domenicaperex1007-pixel/FdD_E_14/Proyecto/Módulo Mecánico/Certificados/Calva Becerra, Sofia/CertificadosUnidos.pdf

Soa Calva

Introduction to Sketching

April 30, 2026

Soa Calva

Introduction to Part Studios

April 30, 2026

Soa Dayanna Calva Becerra

April 30, 2026

Detailed Drawings

Soa Dayanna Calva Becerra

April 30, 2026

Introduction to Onshape Assemblies

Soa Dayanna Calva Becerra

Advanced Onshape Assemblies

May 21, 2026
