domenicaperex1007-pixel/FdD_E_14/Proyecto/Módulo Mecánico/Certificados/Cayco Tucto, Caleb/CertificadosUnidos.pdf

Caleb tucto

Introduction to Sketching

April 30, 2026

Caleb Cayco Tucto

Introduction to Part Studios

April 30, 2026

Caleb Cayco Tucto

April 30, 2026

Detailed Drawings

Caleb Cayco Tucto

April 30, 2026

Introduction to Onshape Assemblies

Caleb Cayco Tucto

Advanced Onshape Assemblies

May 21, 2026
