domenicaperex1007-pixel/FdD_E_14/Proyecto/Módulo Mecánico/Certificados/Dulanto Aguilar, Nemesis/CertificadosUnidos.pdf

Nemesis Krystel Dulanto Aguilar

Introduction to Sketching

April 30, 2026

Nemesis Krystel Dulanto Aguilar

Introduction to Part Studios

April 30, 2026

Nemesis Krystel Dulanto Aguilar

April 30, 2026

Detailed Drawings

Nemesis Krystel Dulanto Aguilar

April 30, 2026

Introduction to Onshape Assemblies

Nemesis Krystel Dulanto Aguilar

Advanced Onshape Assemblies

May 21, 2026
