domenicaperex1007-pixel/FdD_E_14/Proyecto/Módulo Mecánico/Certificados/Huillca Quispe, Kevin/CertificadosUnidos.pdf

Kevin Huillca

Introduction to Sketching

April 30, 2026

Kevin Huillca

Introduction to Part Studios

April 30, 2026

Kevin Huillca

April 30, 2026

Detailed Drawings

Kevin Huillca

April 30, 2026

Introduction to Onshape Assemblies

Kevin Huillca

Advanced Onshape Assemblies

May 21, 2026
