domenicaperex1007-pixel/FdD_E_14/Proyecto/Módulo Mecánico/Certificados/Perez Suarez, Doménica/CertificadosUnidos.pdf

Doménica Tiziana Ximena Pérez Suárez

Introduction to Sketching

April 30, 2026

Doménica Tiziana Ximena Pérez Suárez

Introduction to Part Studios

April 30, 2026

Doménica Tiziana Ximena Pérez Suárez

April 30, 2026

Detailed Drawings

Doménica Tiziana Ximena Pérez Suárez

April 30, 2026

Introduction to Onshape Assemblies

Doménica Tiziana Ximena Pérez Suárez

Advanced Onshape Assemblies

May 21, 2026
