domenicaperex1007-pixel/FdD_E_14/Proyecto/Módulo Mecánico/V1.0/Bocetos/Boceto isométricoA V1.0.png

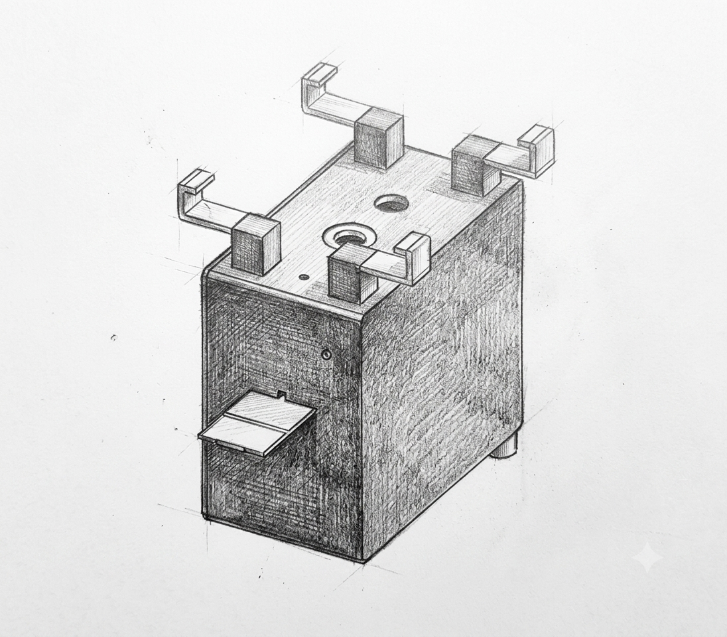
Proyecto/Módulo Mecánico/V1.0/Bocetos/Boceto isométricoA V1.0.png
