domenicaperex1007-pixel/FdD_E_14/Proyecto/Módulo Mecánico/VFINAL/Bocetos/Boceto isométricoA VFINAL.png

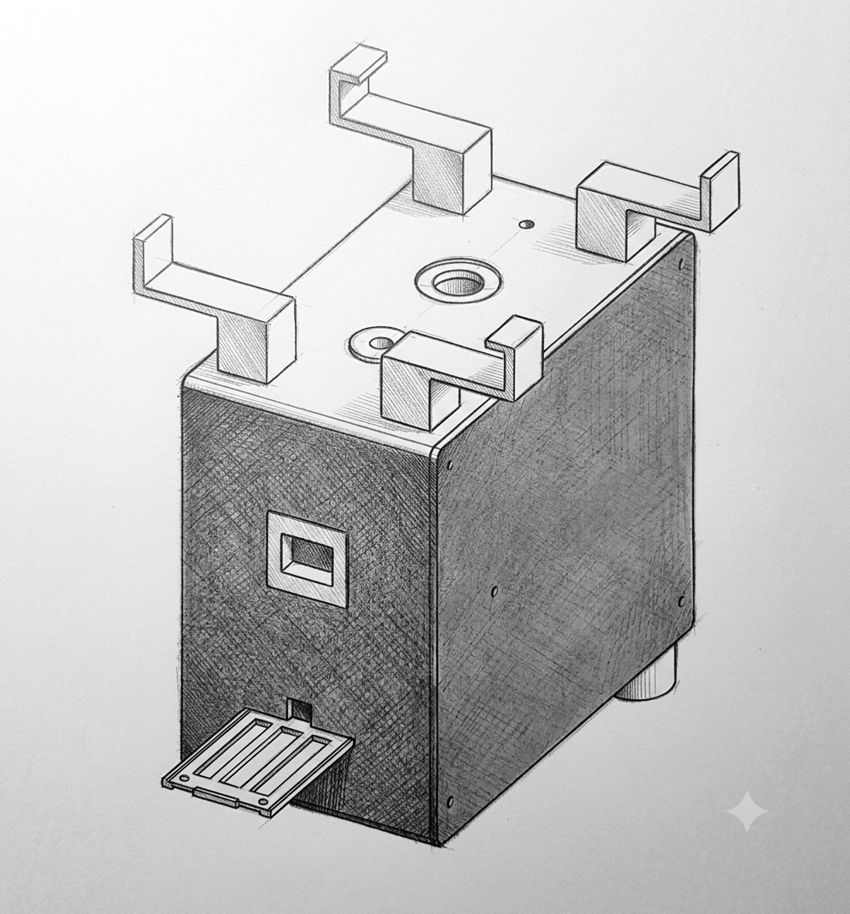
Proyecto/Módulo Mecánico/VFINAL/Bocetos/Boceto isométricoA VFINAL.png
