domenicaperex1007-pixel/FdD_E_14/Proyecto/Módulo Electrónico/V2.0/Esquemático V2.0.pdf

# ESP 32

R1

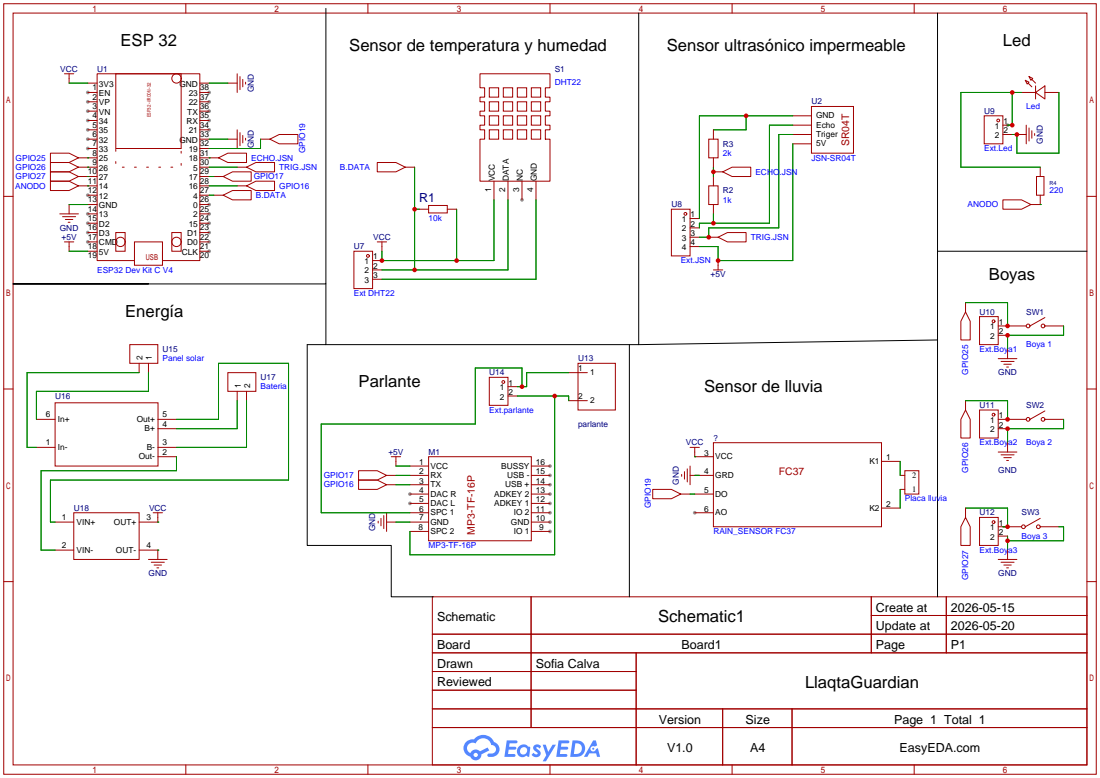
[picture p65: page 1]
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

Schematic | Schematic1 | Create at | 2026-05-15

Update at | 2026-05-20

Board | Board1 | Page | P1
Drawn | Sofia Calva | LlaqtaGuardian
Reviewed

Version | Size | Page 1 Total 1
V1.0 | A4 | EasyEDA.com
