domenicaperex1007-pixel/FdD_E_14/Proyecto/Módulo Mecánico/V1.0/Onshape/Planos/Plano_Estructura en L V1.0.pdf

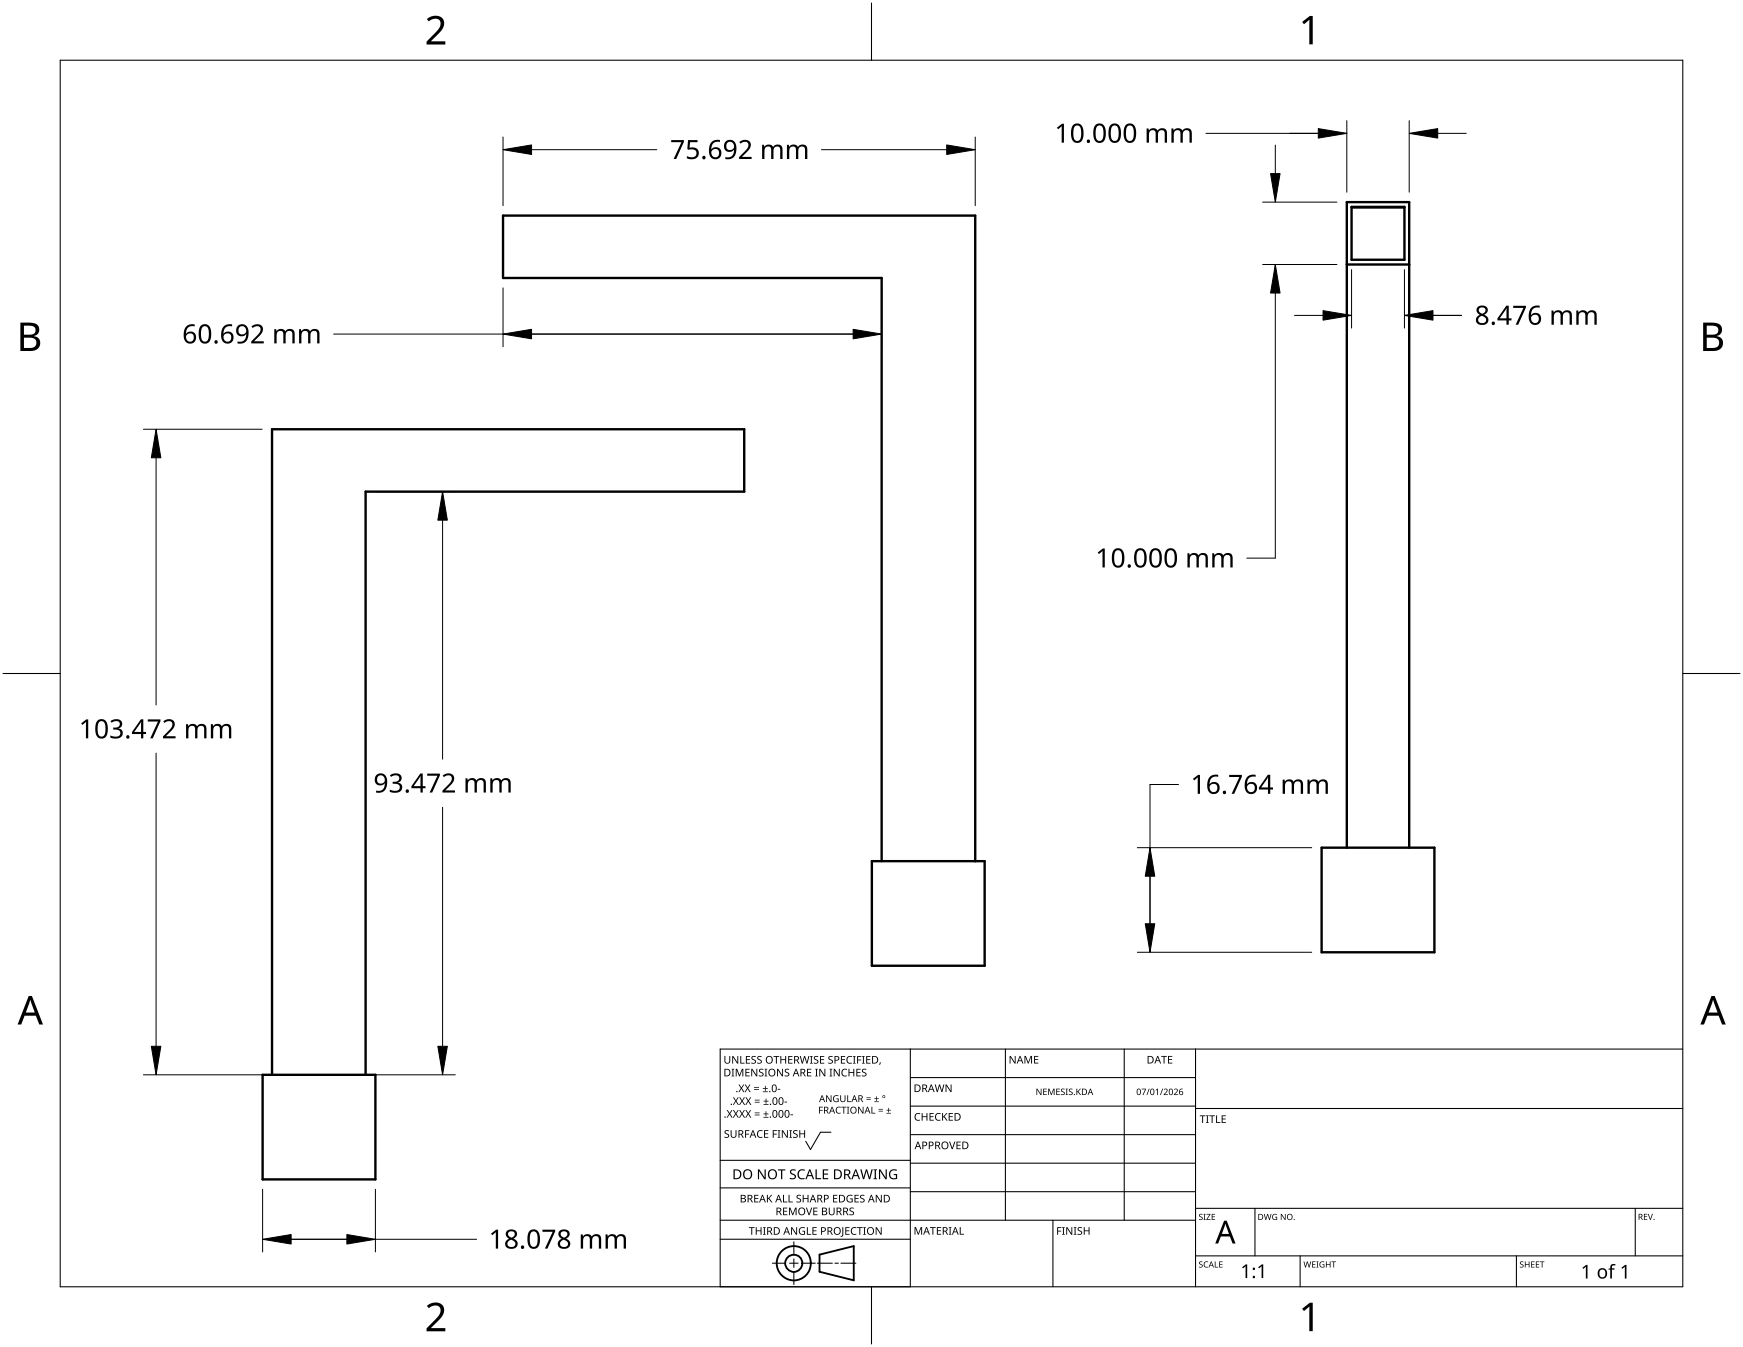
[picture p71: page 1]
