domenicaperex1007-pixel/FdD_E_14/Proyecto/Módulo Mecánico/V1.0/Onshape/Planos/Plano_SoporteFC37 V1.0.pdf

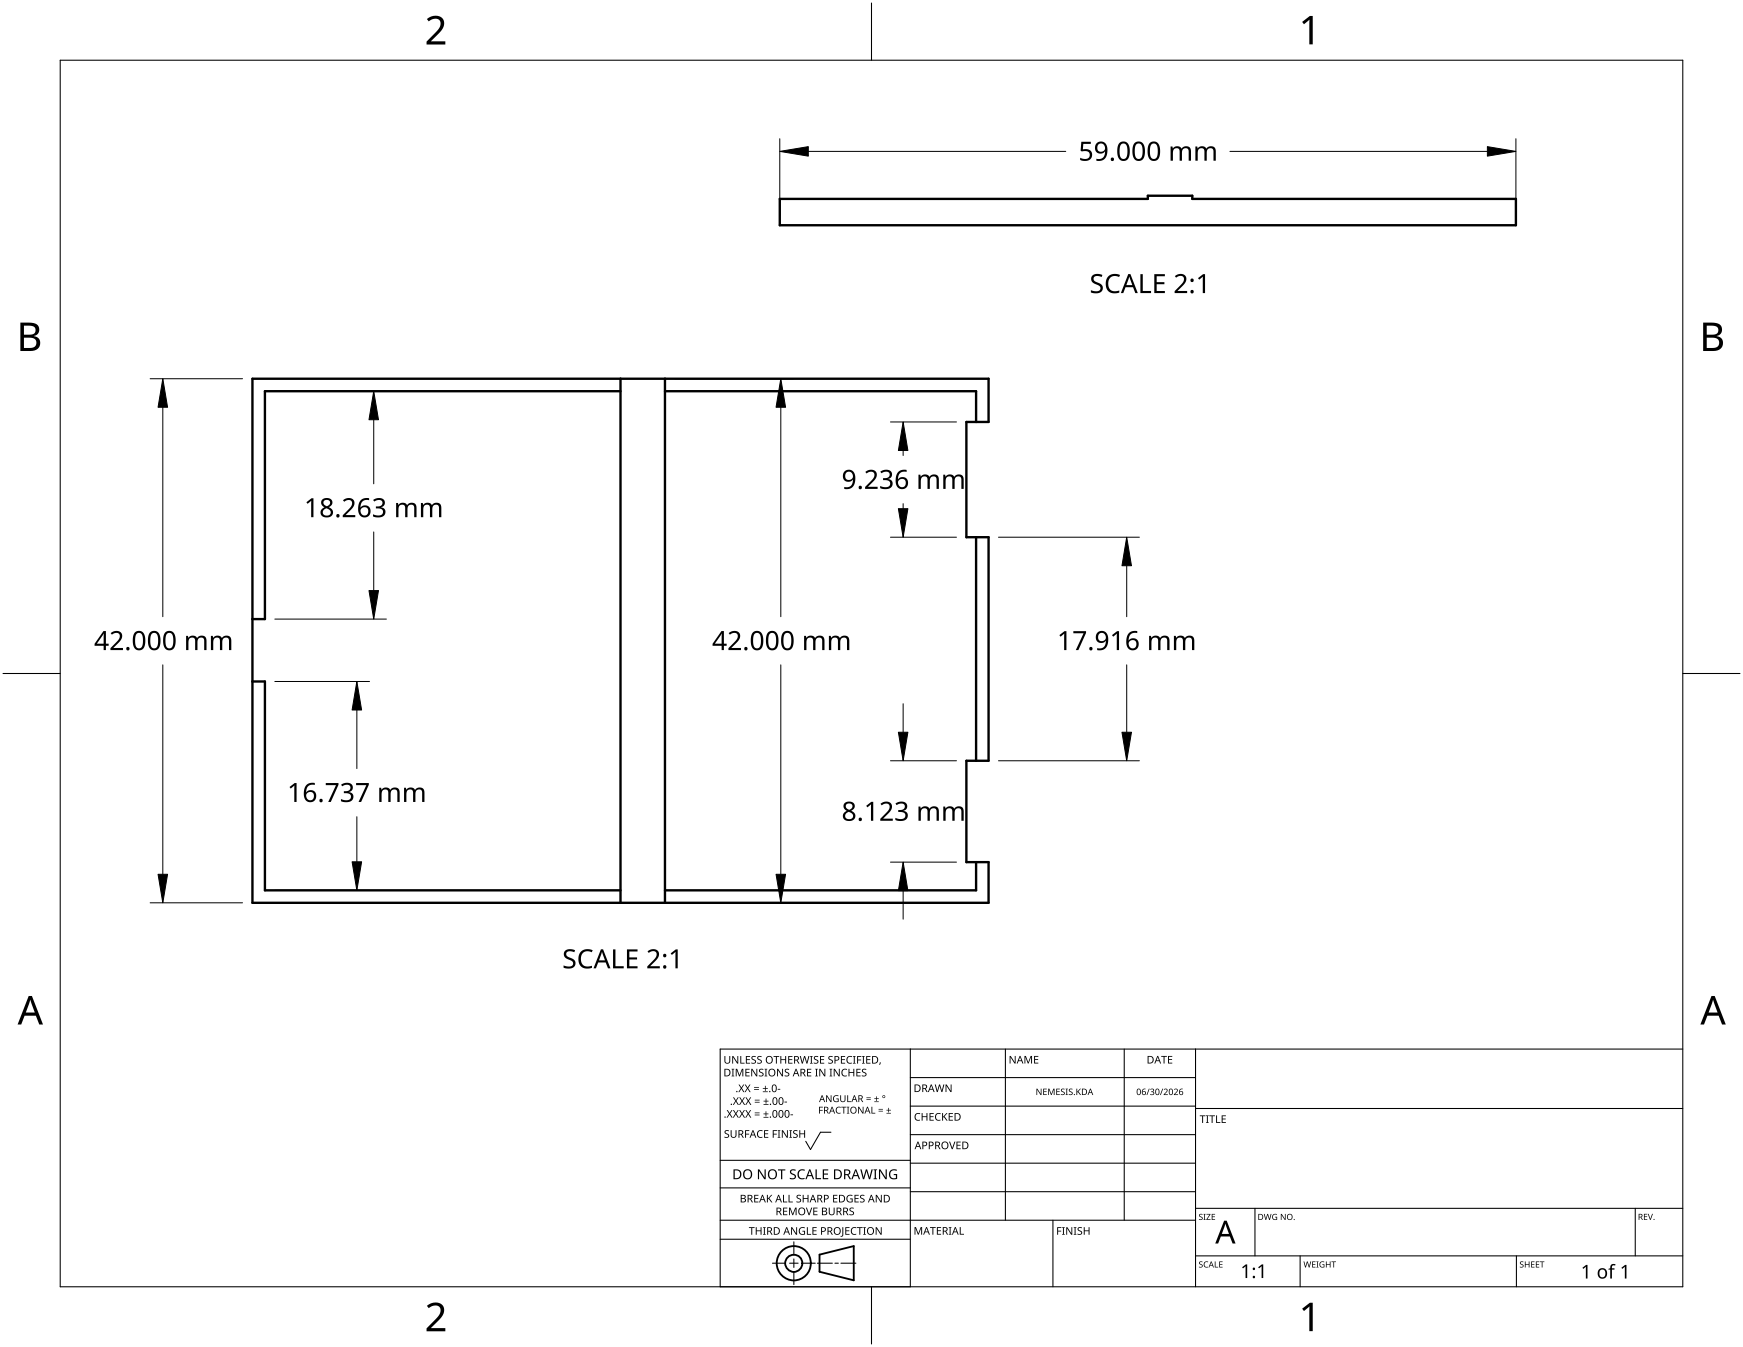
[picture p72: page 1]
