domenicaperex1007-pixel/FdD_E_14/Proyecto/Módulo Mecánico/V1.0/Onshape/Planos/Plano_Caja V1.0.pdf

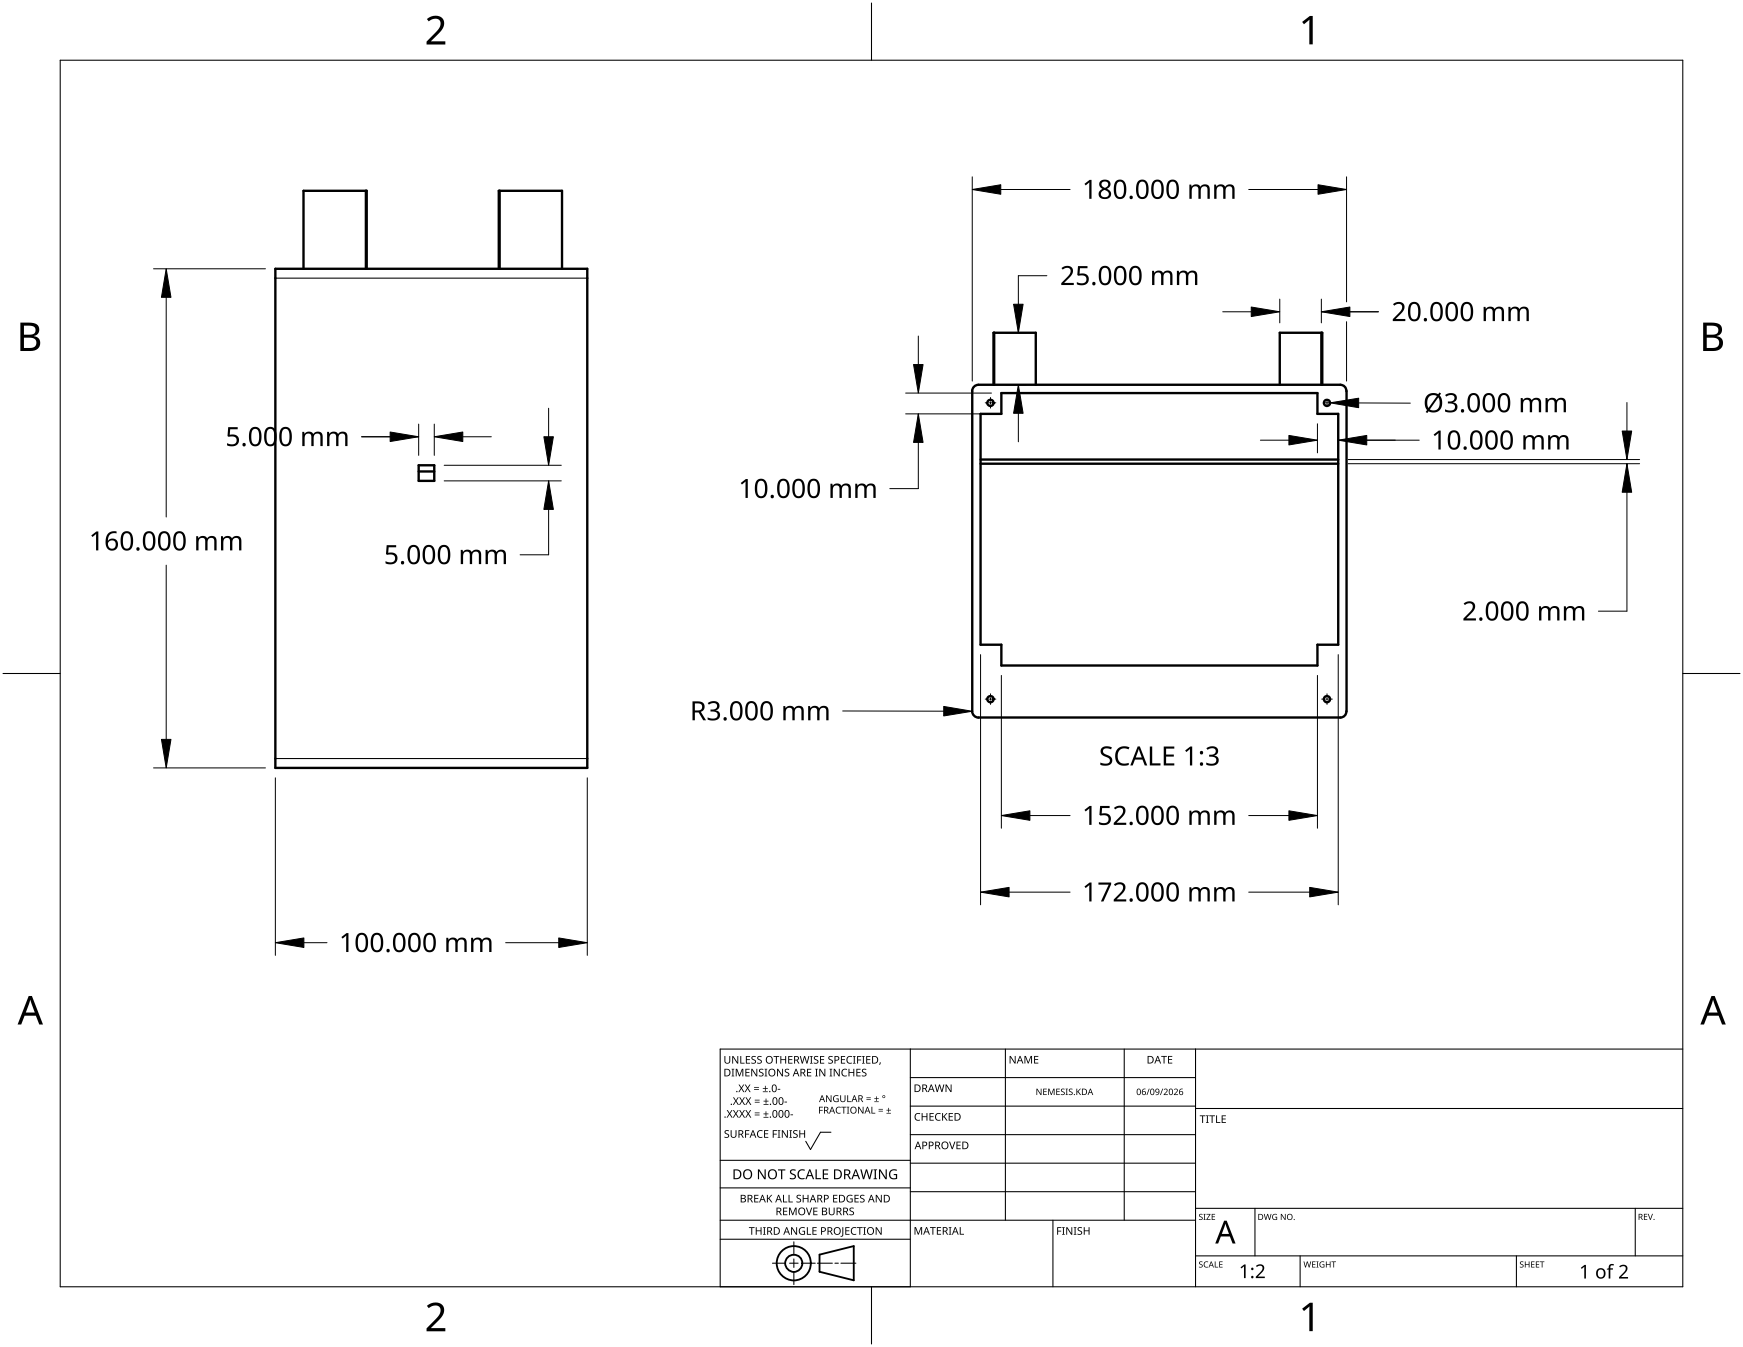
[picture p73: page 1]

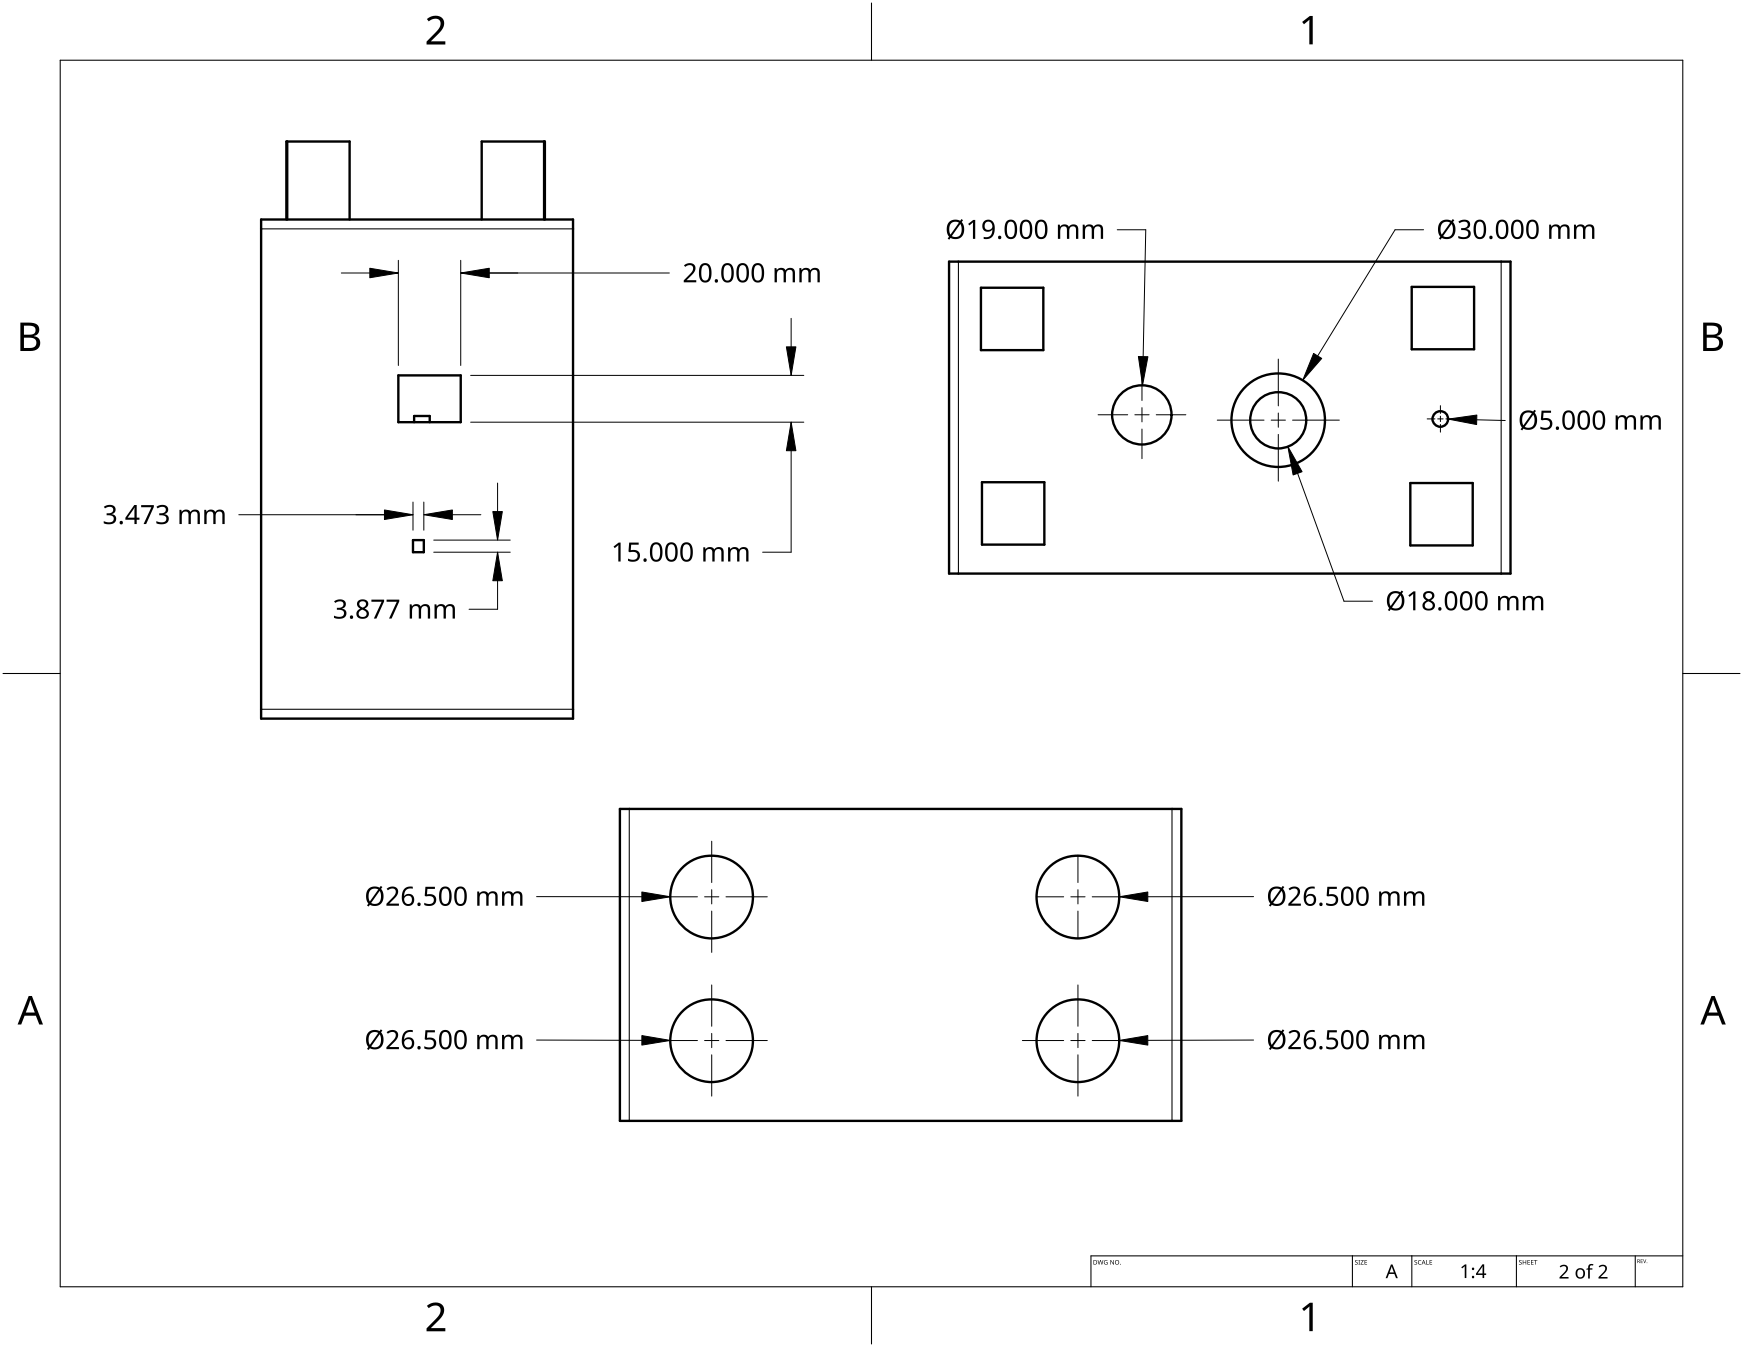
[picture p74: page 2]
