domenicaperex1007-pixel/FdD_E_14/Proyecto/Módulo Mecánico/V1.0/Onshape/Planos/Plano_Puerta V1.0.pdf

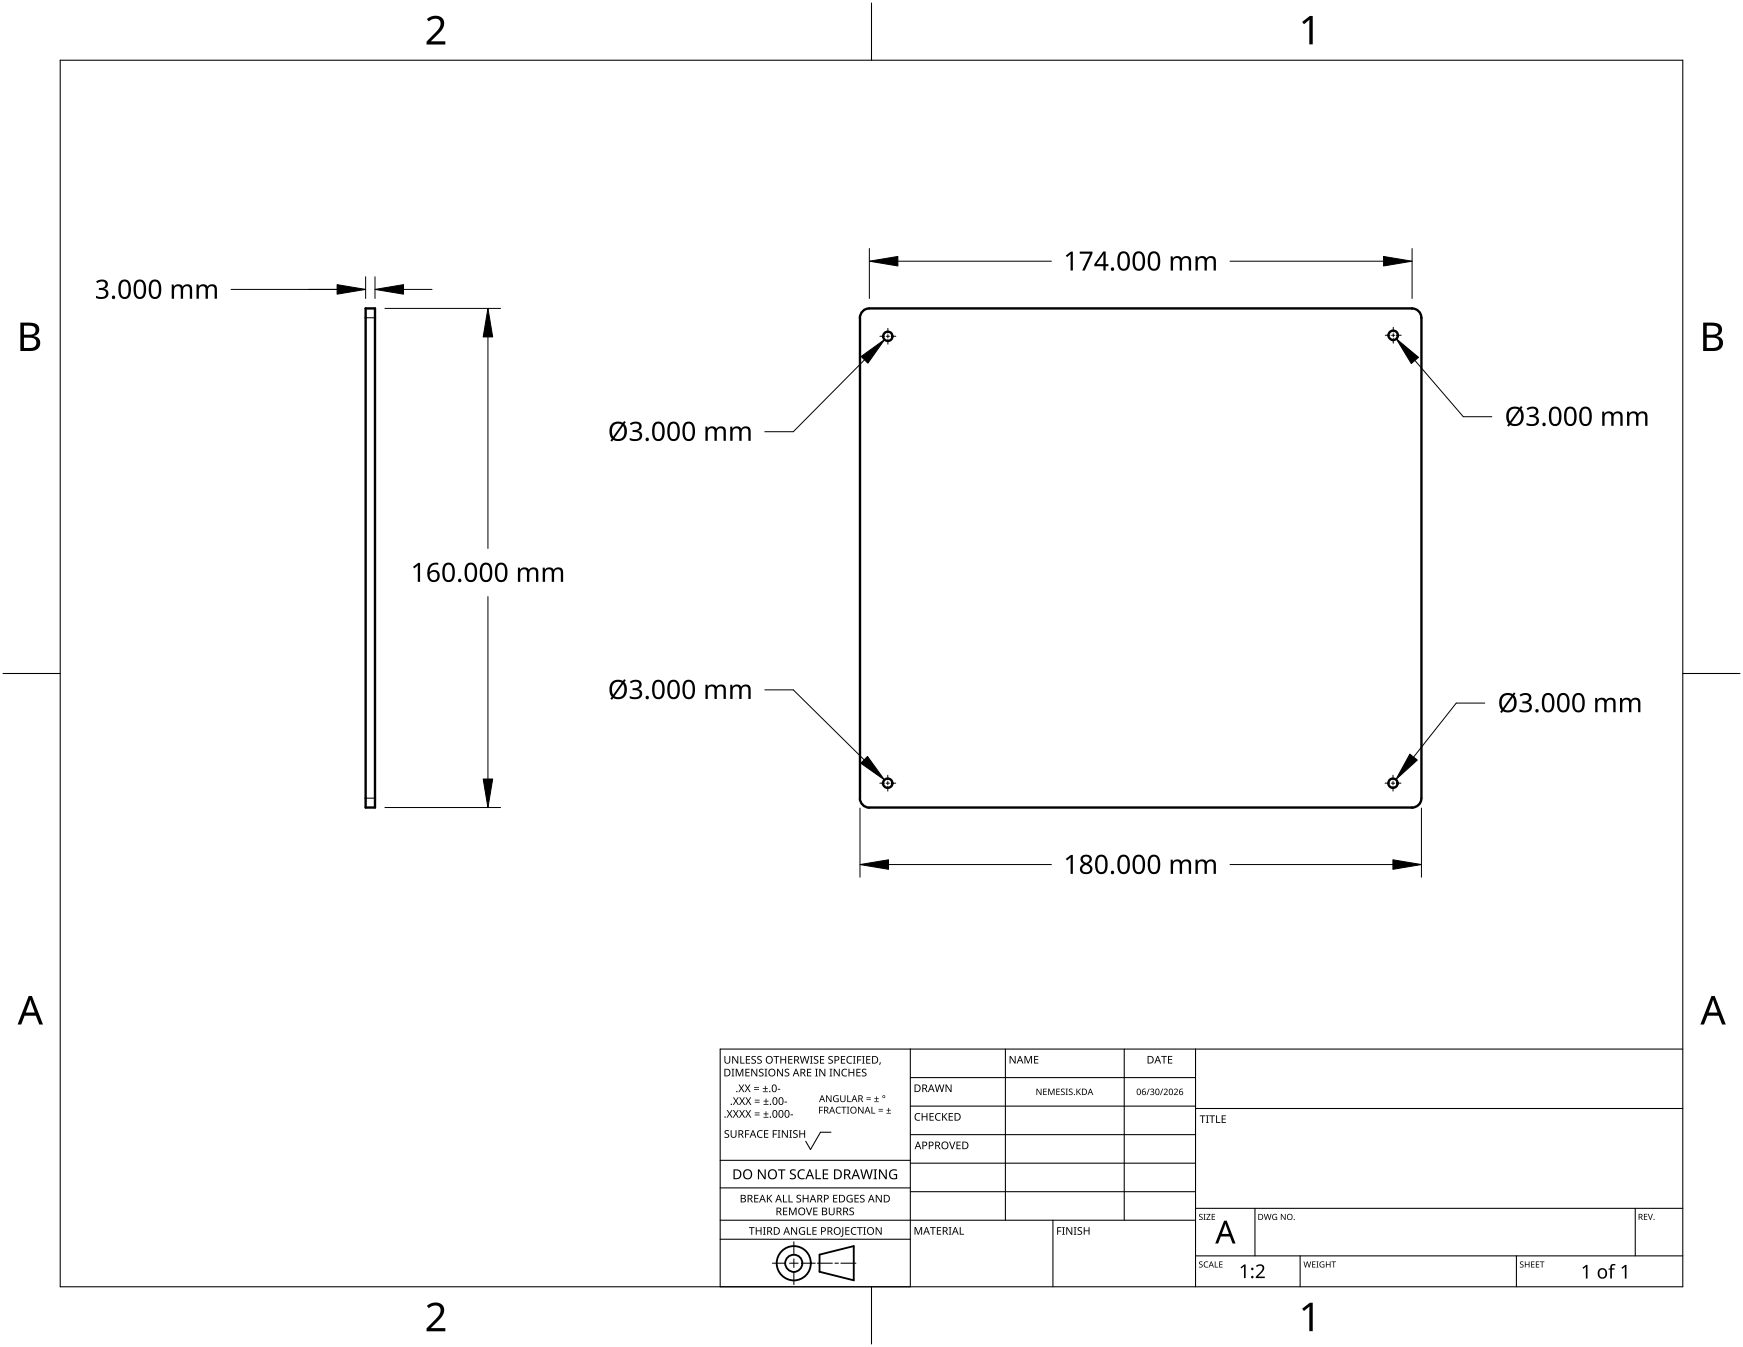
[picture p75: page 1]
