domenicaperex1007-pixel/FdD_E_14/Proyecto/Módulo Mecánico/VFINAL/Onshape/Planos/Plano_Caja VFINAL.pdf

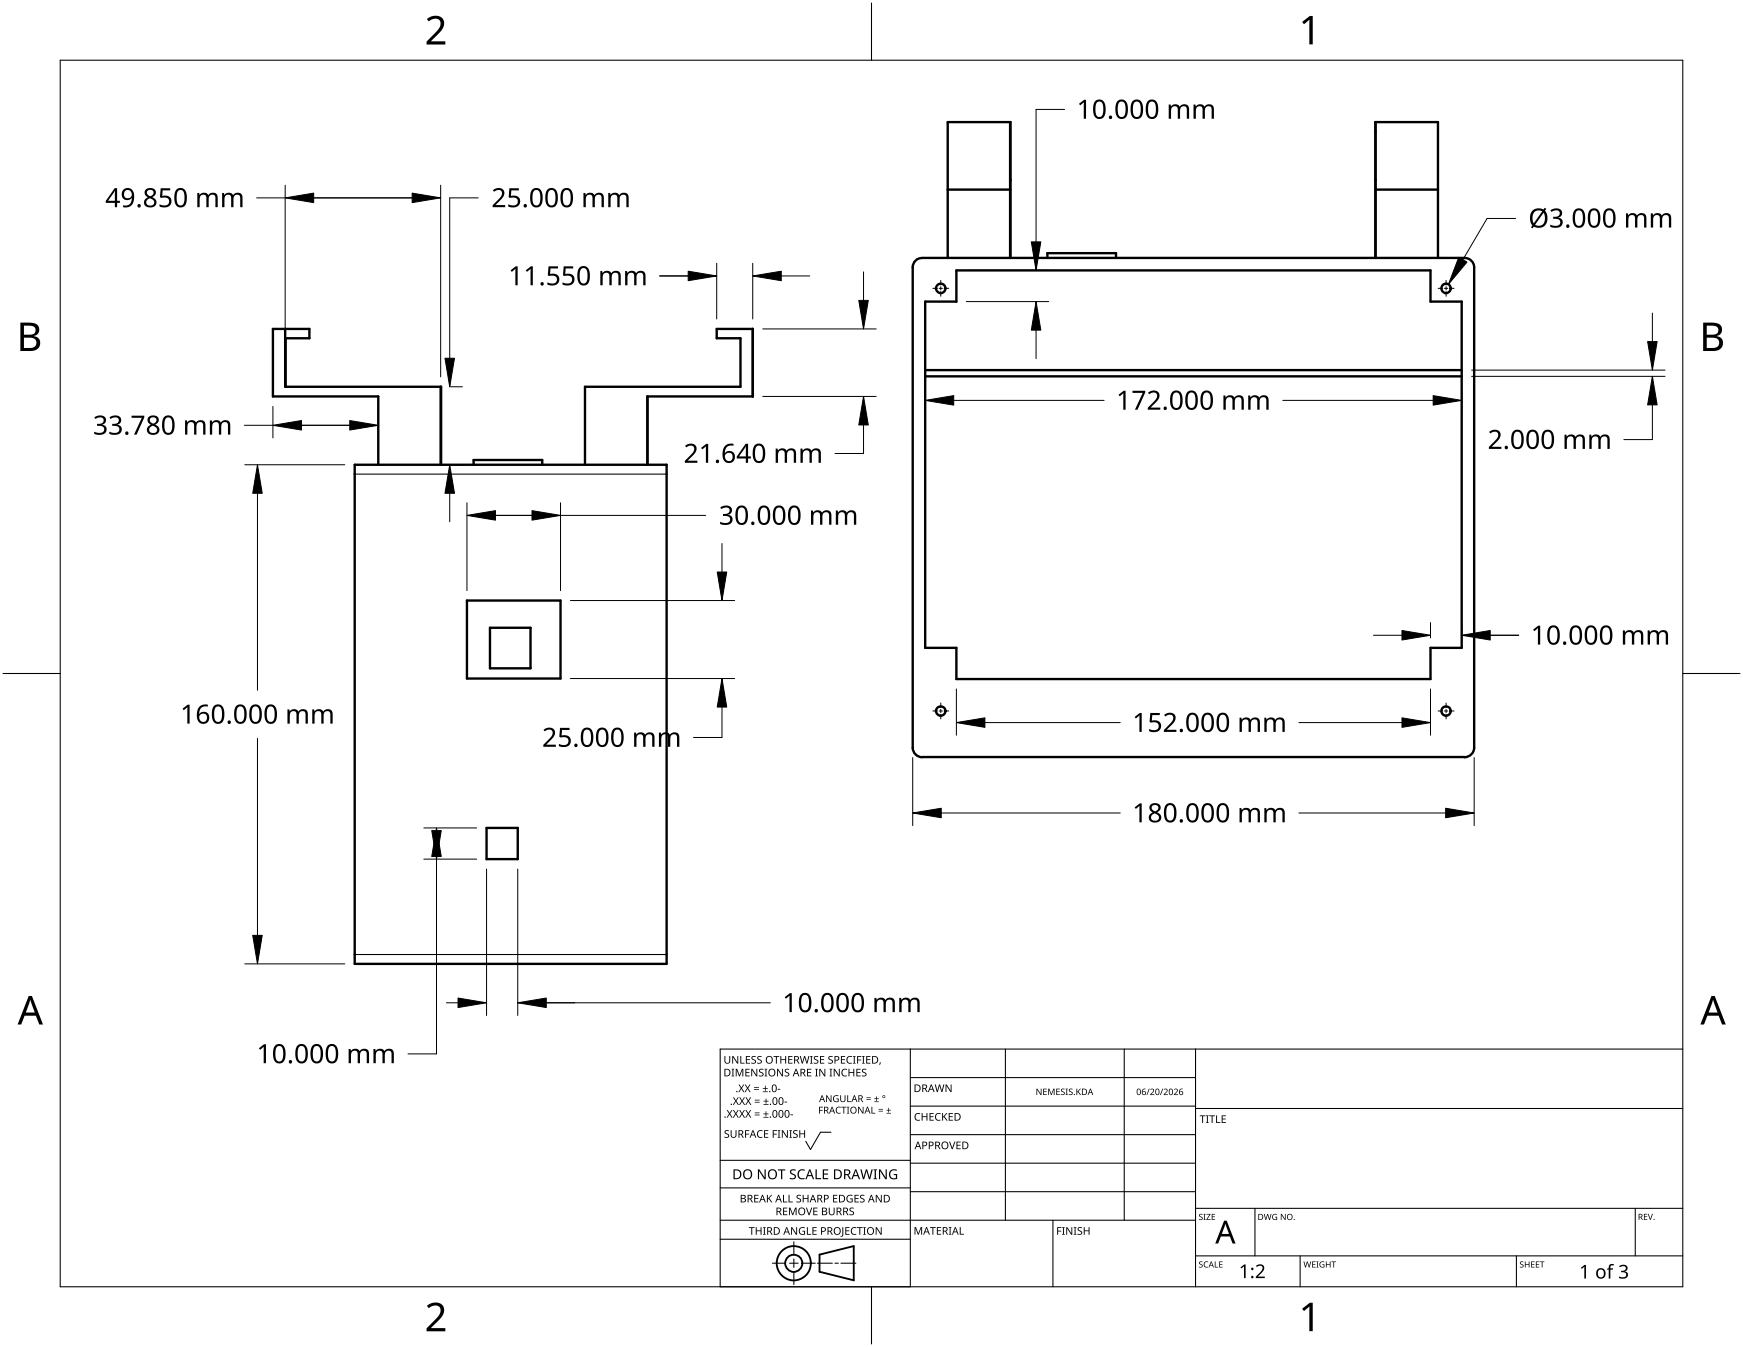
[picture p76: page 1]

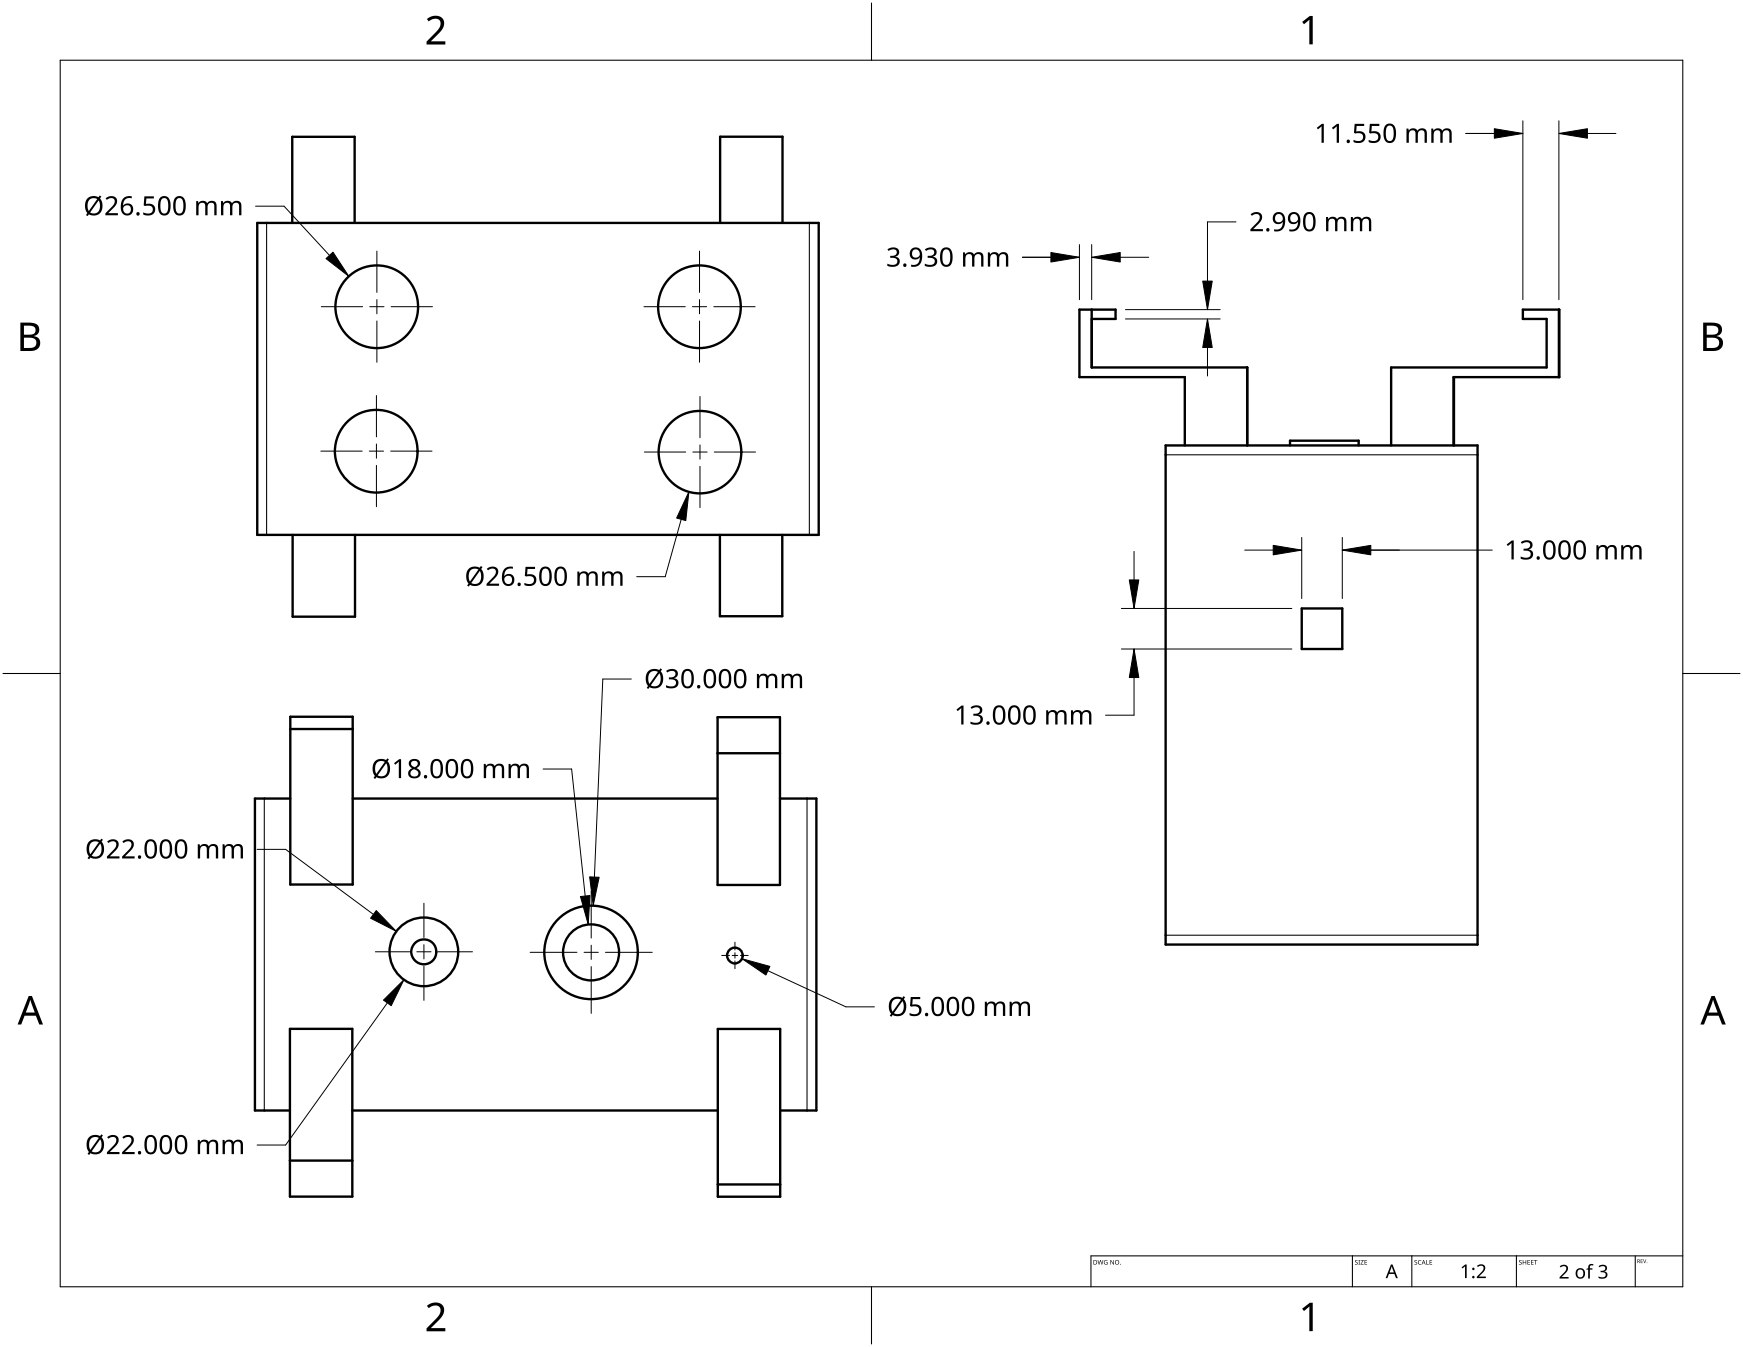
[picture p77: page 2]

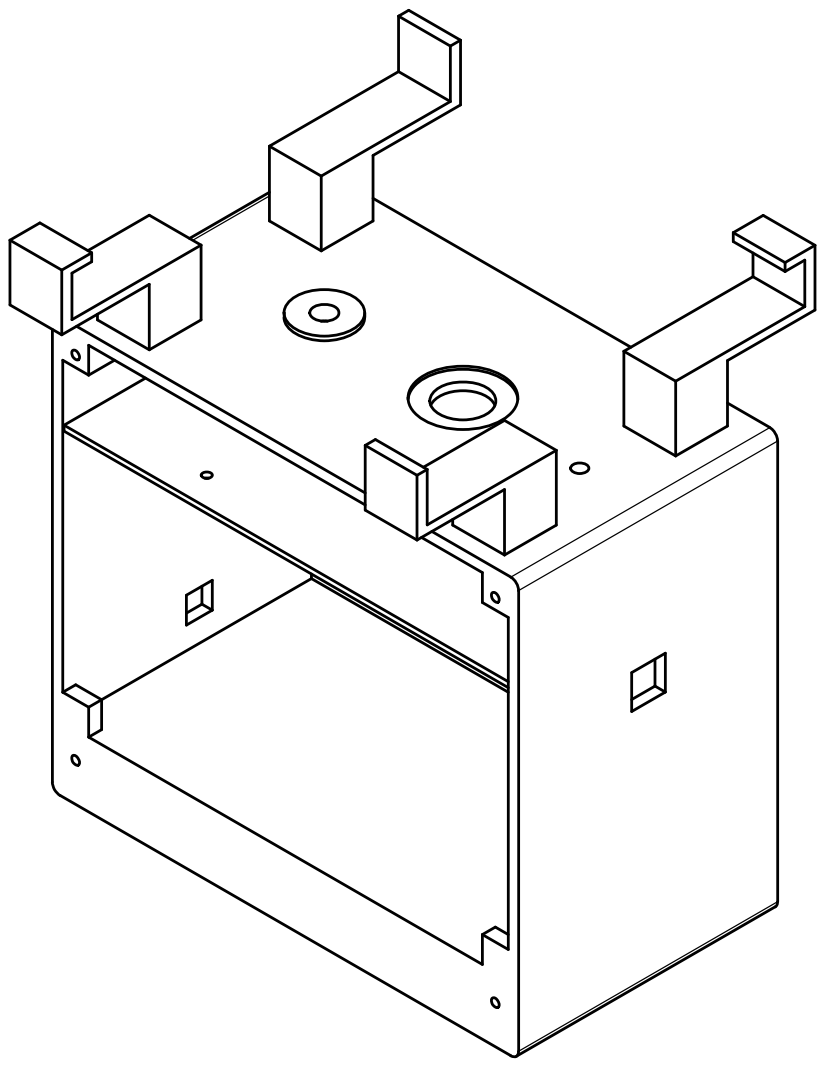
[picture p78: page 3]
