domenicaperex1007-pixel/FdD_E_14/Proyecto/Módulo Mecánico/VFINAL/Onshape/Planos/Plano_Dona VFINAL.pdf

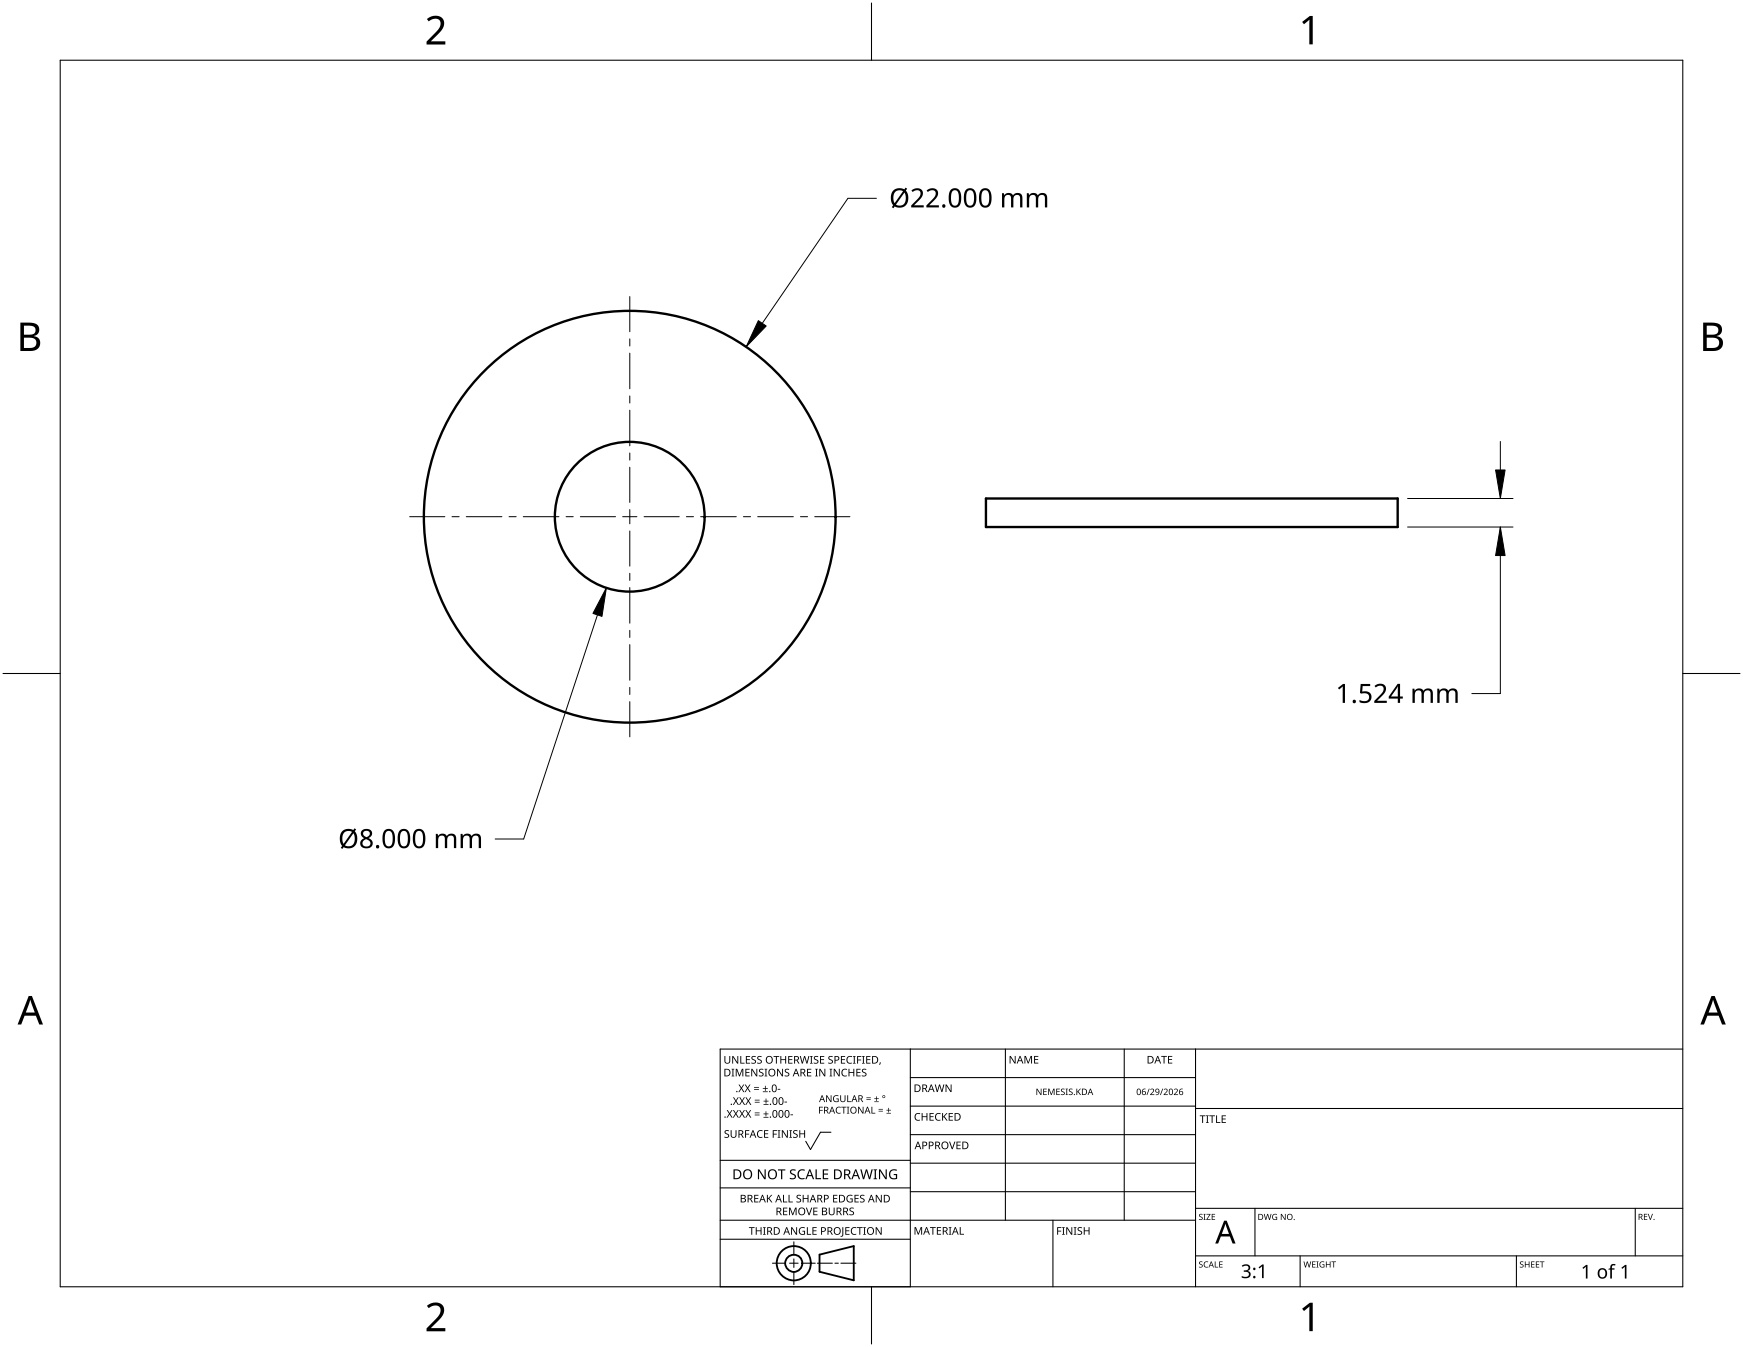
[picture p79: page 1]
