domenicaperex1007-pixel/FdD_E_14/Proyecto/Módulo Mecánico/VFINAL/Onshape/Planos/Plano_Estaca VFINAL.pdf

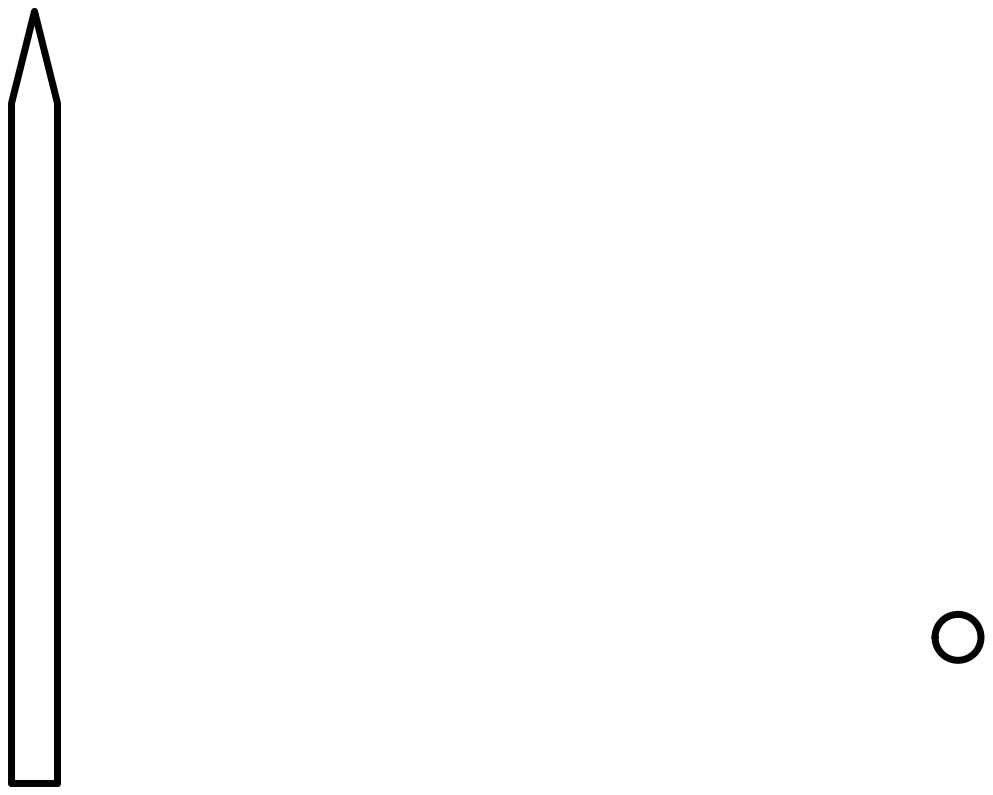
[picture p80: page 1]
