domenicaperex1007-pixel/FdD_E_14/Proyecto/Módulo Mecánico/VFINAL/Onshape/Planos/Plano_Estructura en L VFINAL.pdf

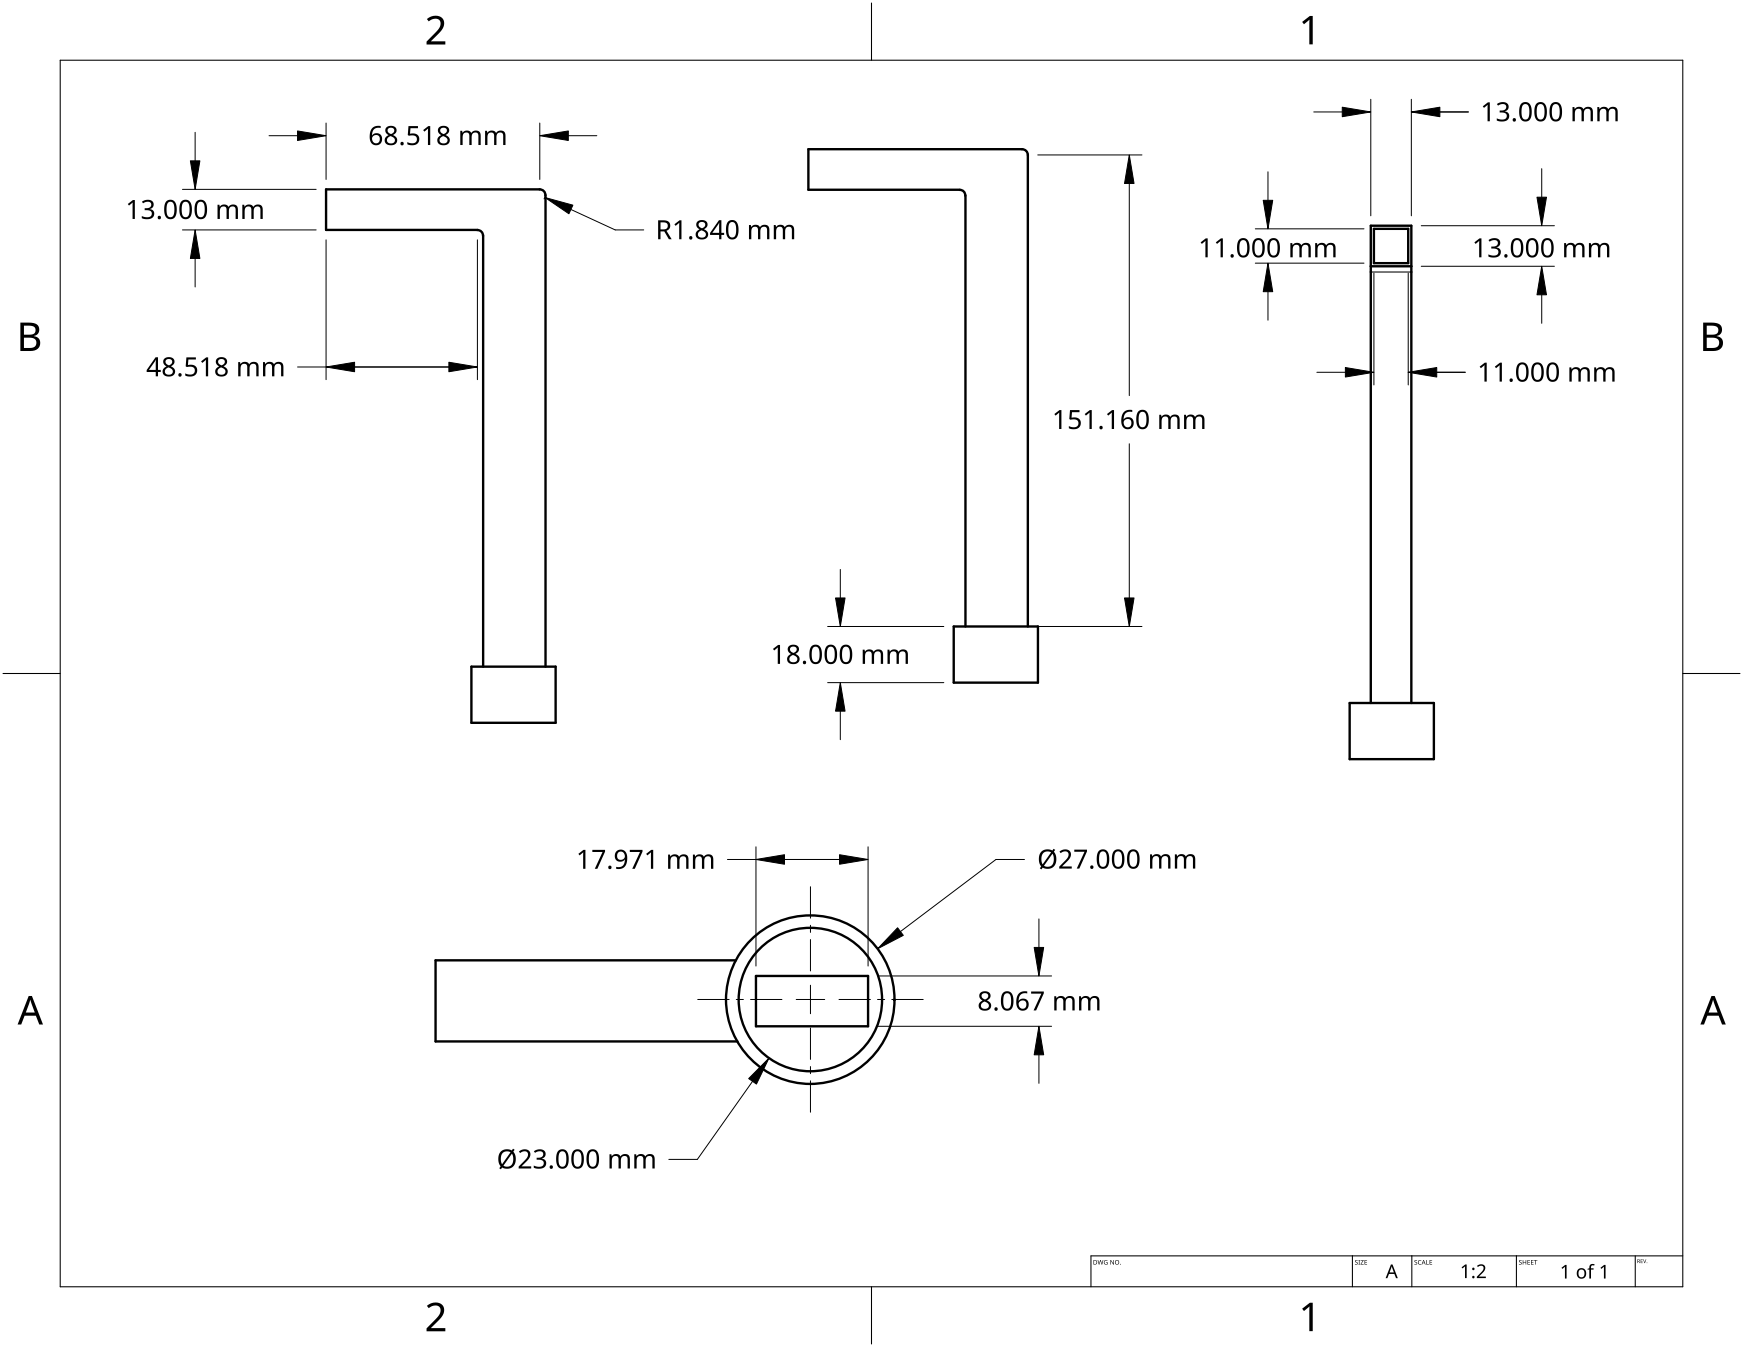
[picture p81: page 1]
