domenicaperex1007-pixel/FdD_E_14/Proyecto/Módulo Mecánico/VFINAL/Onshape/Planos/Plano_Puerta VFINAL.pdf

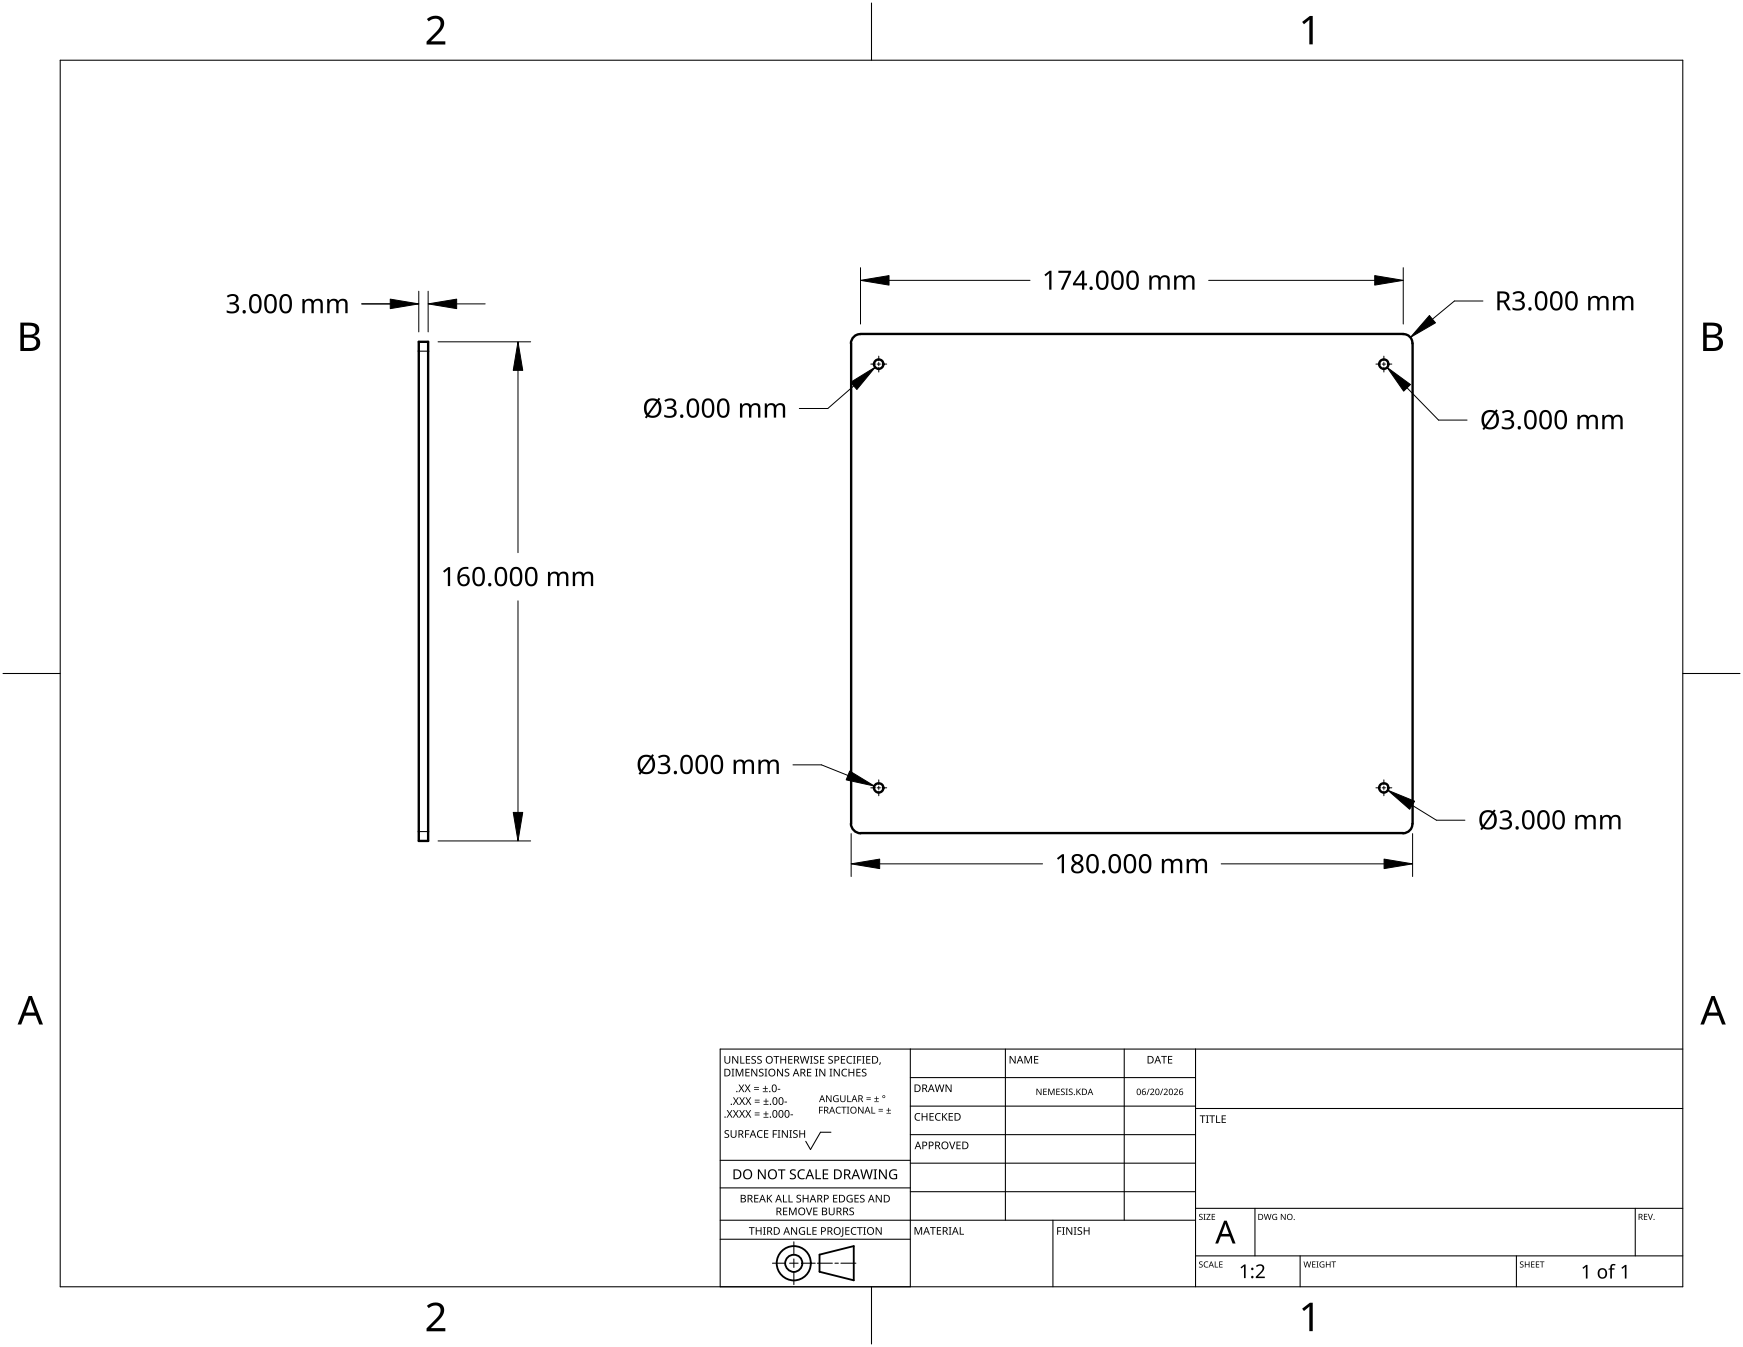
[picture p82: page 1]
