domenicaperex1007-pixel/FdD_E_14/Proyecto/Módulo Mecánico/VFINAL/Onshape/Planos/Plano_SoporteFC37 VFINAL.pdf

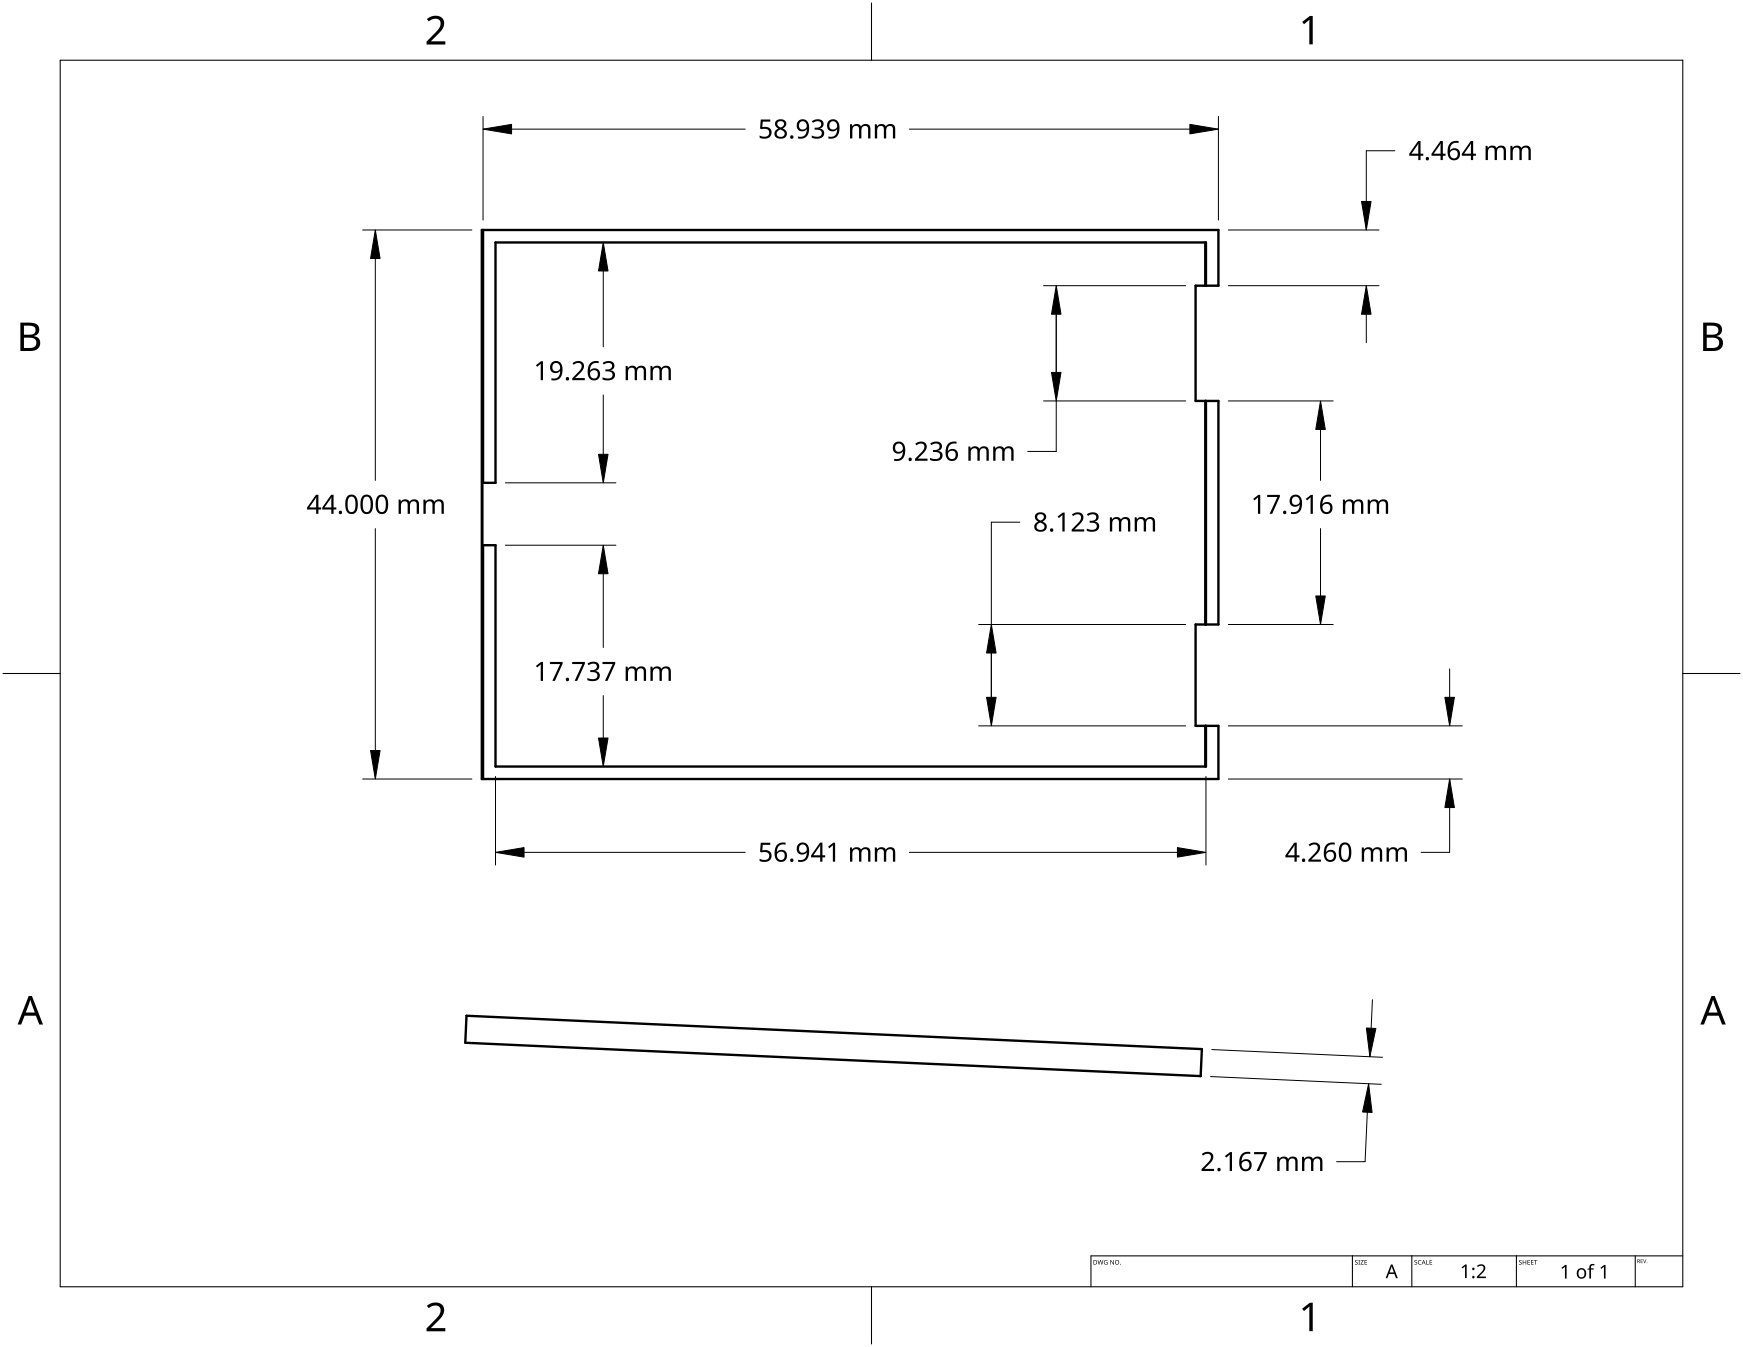
[picture p83: page 1]
