domenicaperex1007-pixel/FdD_E_14/Proyecto/Módulo Mecánico/VFINAL/Onshape/Planos/Plano_Ventana VFINAL.pdf

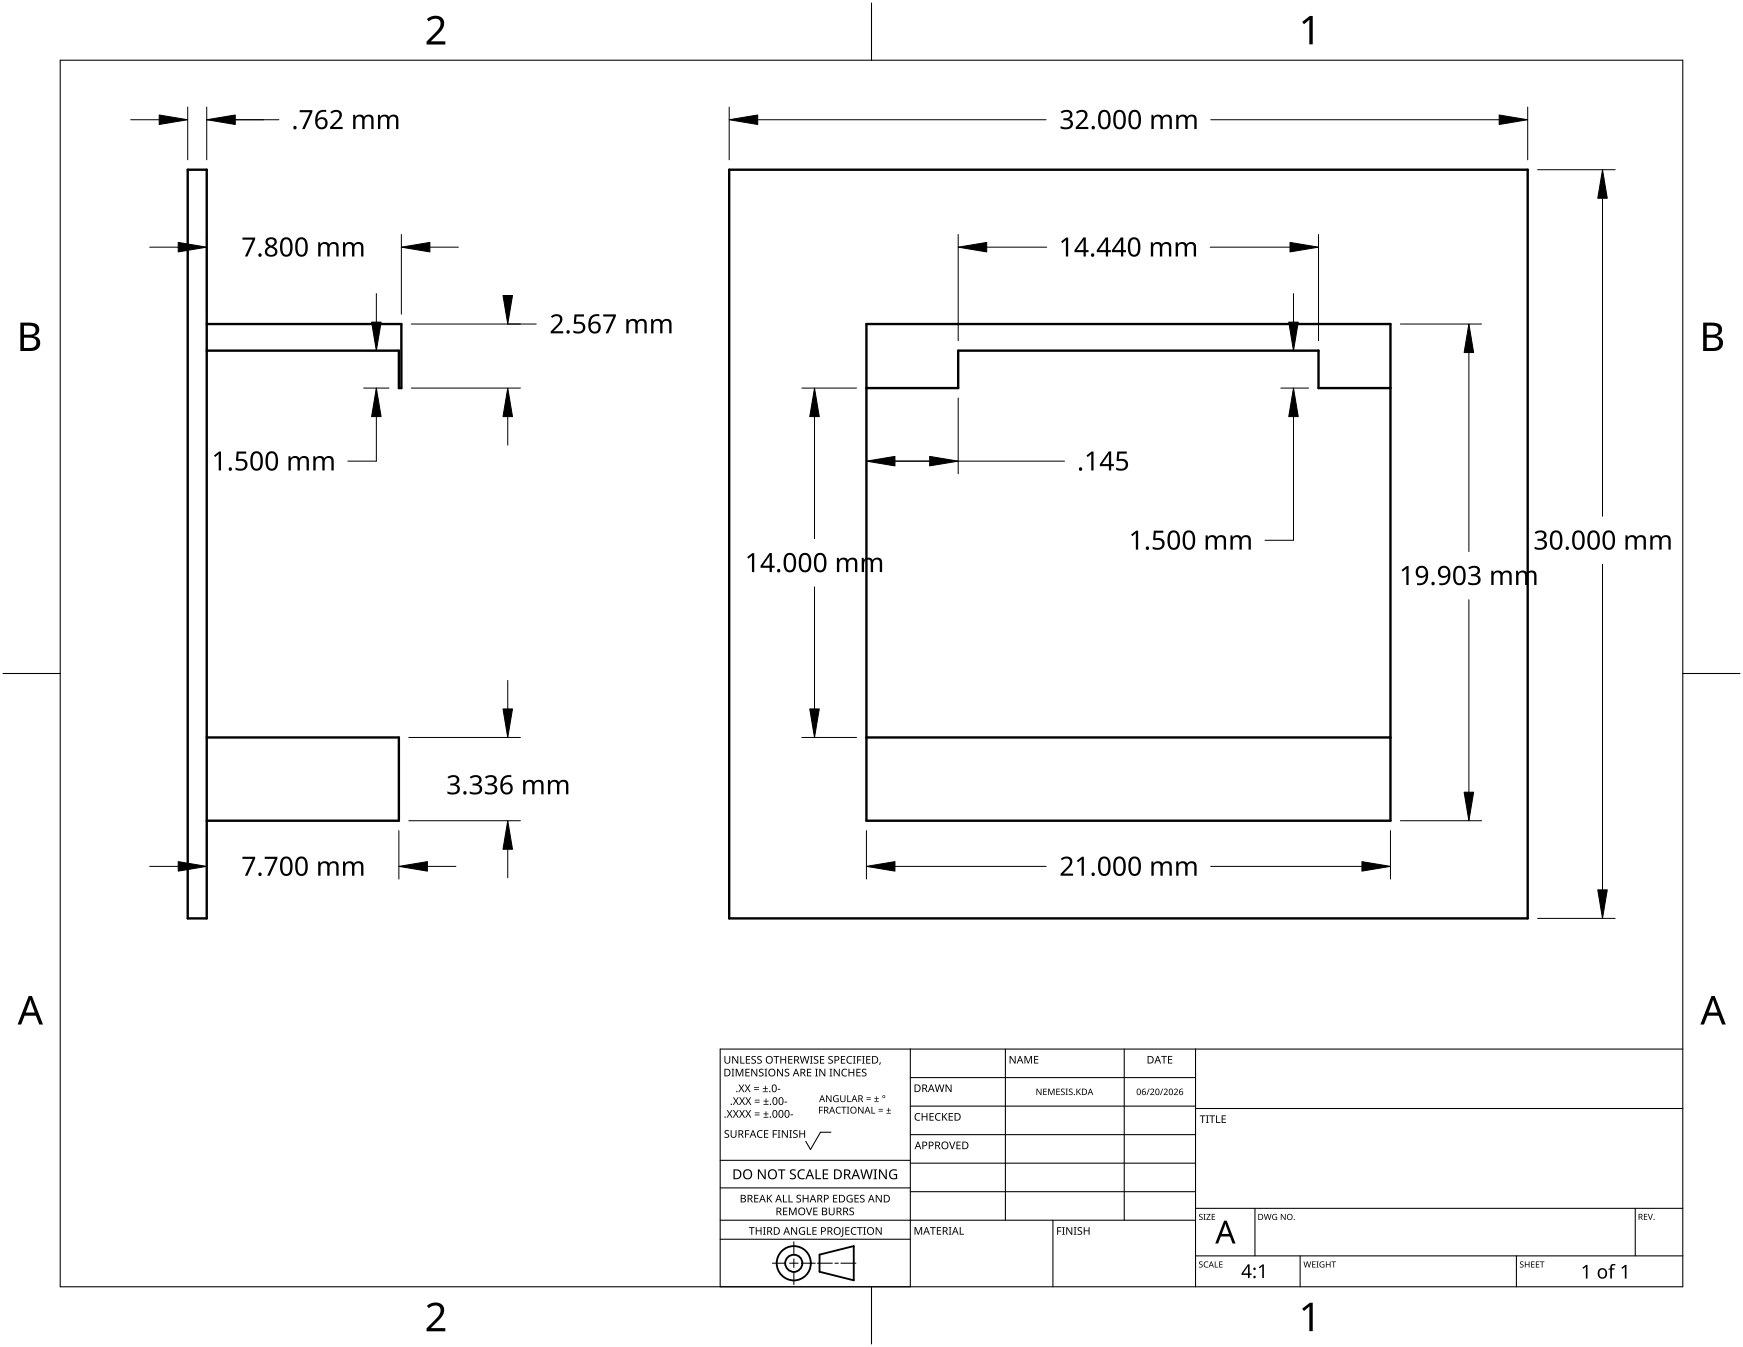
[picture p84: page 1]
